mlab-modules/USB232R02/doc/img/USB232R02A_bot.png

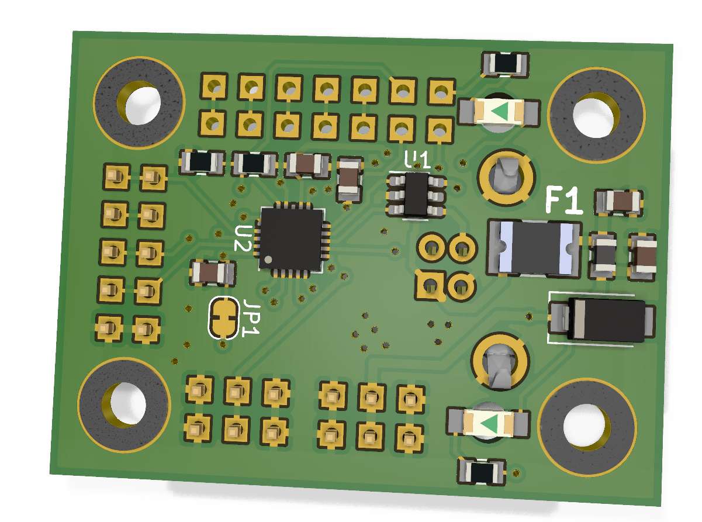
doc/img/USB232R02A_bot.png
